sciguy14/Control-my-Cap/wrist_controller/sample_config.py

#LOCAL MYSQL DATABASE INFO
local_host = 'localhost'
local_user = 'db_username'
local_passwd = 'db_password'
local_db = 'db_name'

#Twitter API Info
CONSUMER_KEY = 'your consumer key'
CONSUMER_SECRET = 'your consumer secret'
